patniemeyer/phone-holder/Media/curved2.png

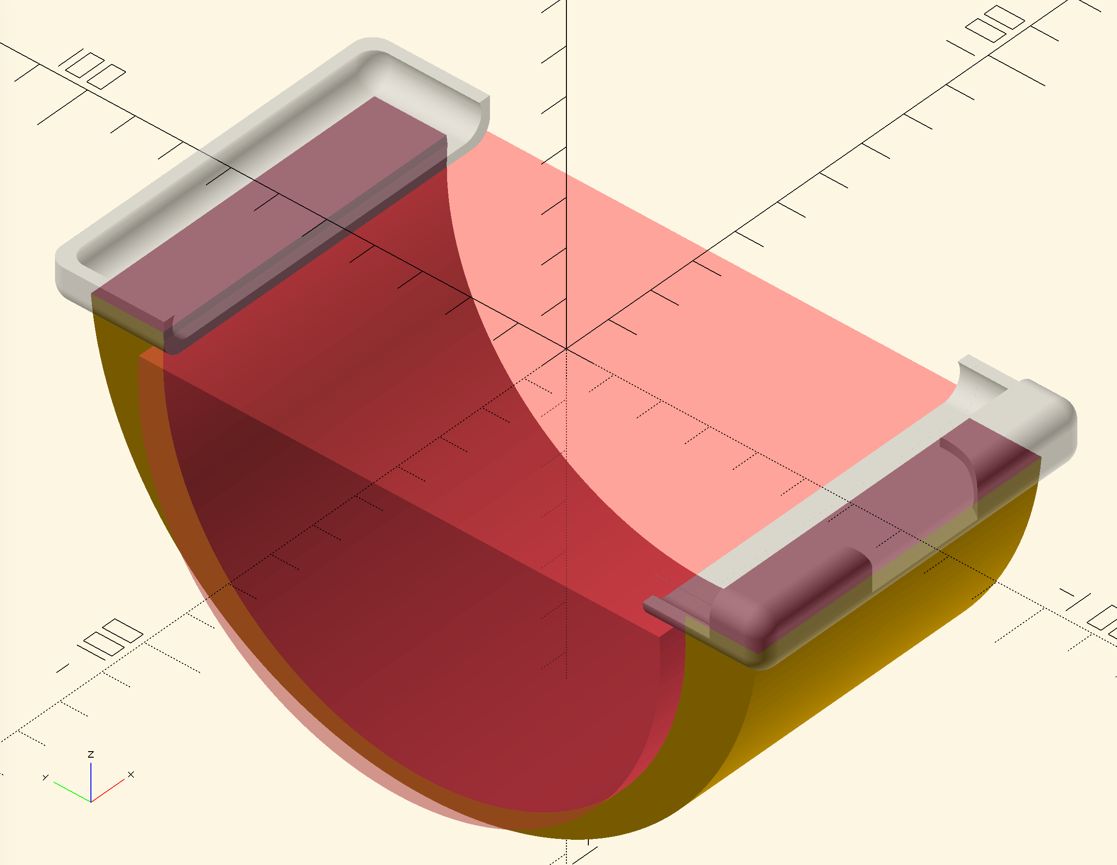
Media/curved2.png
