patniemeyer/phone-holder/Media/IMG_8226.jpg

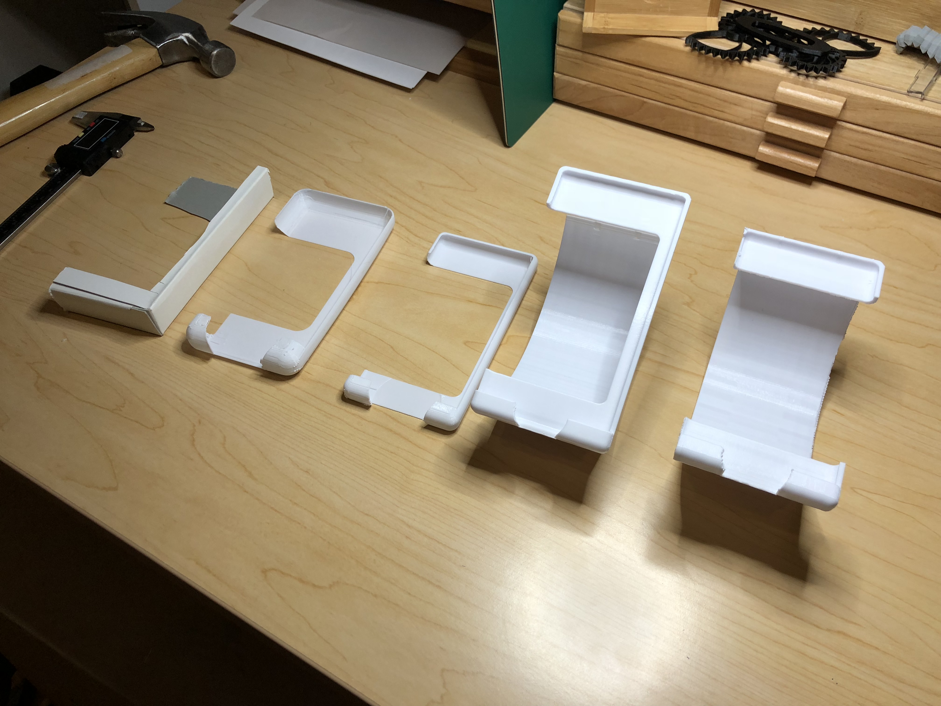
Media/IMG_8226.jpg
