patniemeyer/phone-holder/Media/IMG_9333.jpg

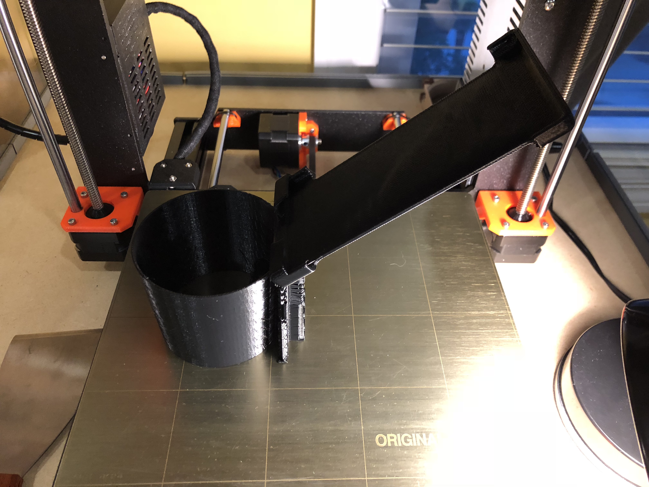
Media/IMG_9333.jpg
