patniemeyer/phone-holder/Media/IMG_9492.jpg

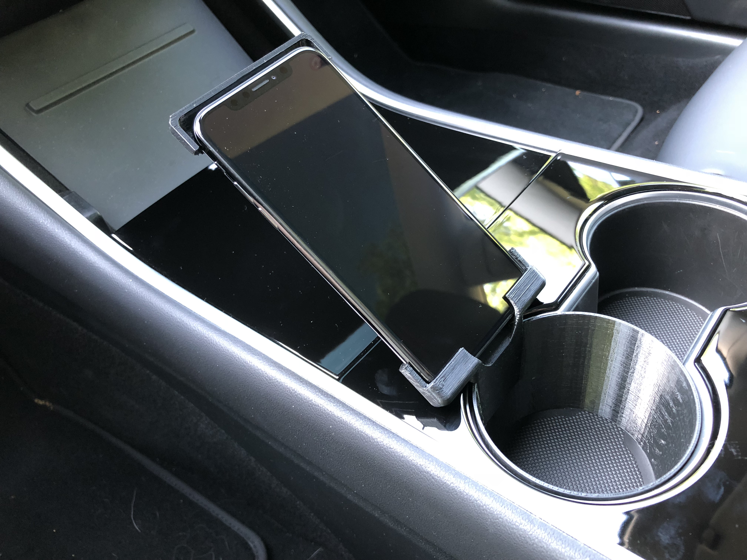
Media/IMG_9492.jpg
