patniemeyer/phone-holder/Media/prototypes2.jpg

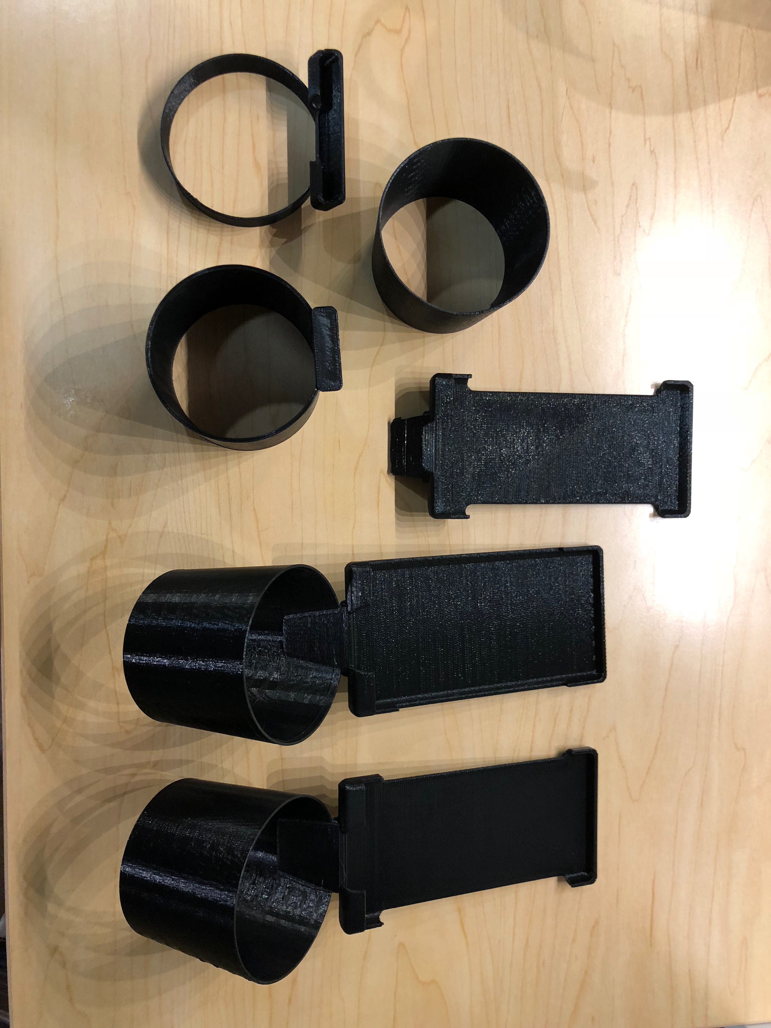
Media/prototypes2.jpg
