patniemeyer/phone-holder/Media/Screen Shot 2018-03-03 at 1.36.28 PM.png

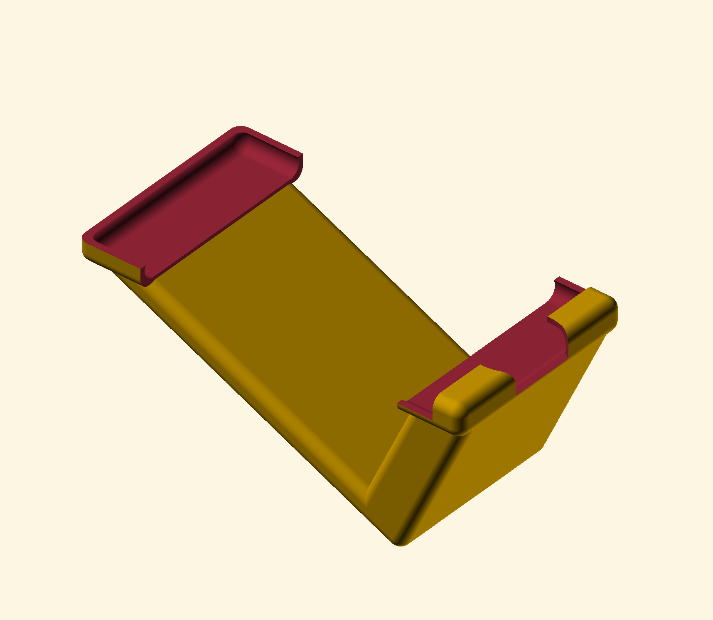
Media/Screen Shot 2018-03-03 at 1.36.28 PM.png
