patniemeyer/phone-holder/Media/Screen Shot 2018-05-19 at 3.50.58 PM.png

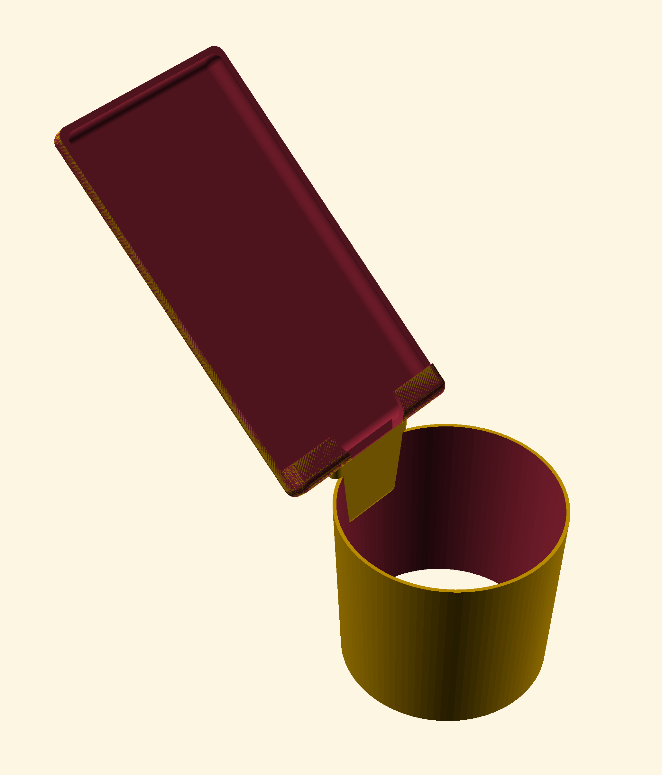
Media/Screen Shot 2018-05-19 at 3.50.58 PM.png
