patniemeyer/phone-holder/Media/wall-holder1.jpg

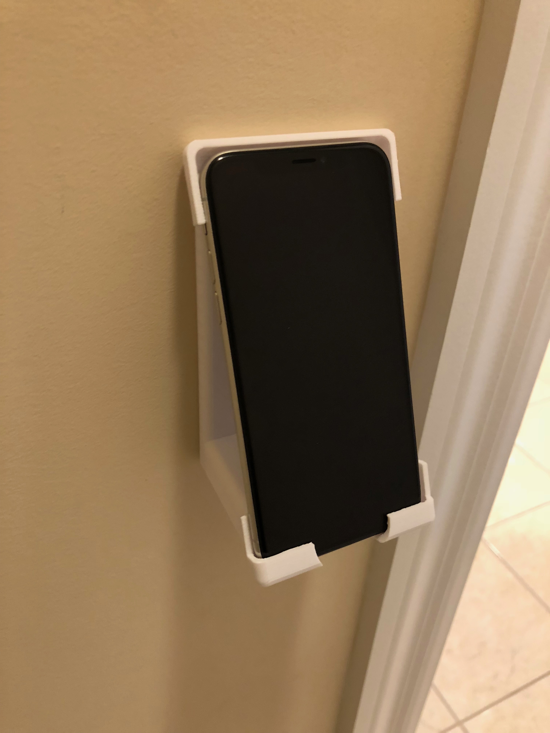
Media/wall-holder1.jpg
