patniemeyer/phone-holder/Media/wall-holder2.jpg

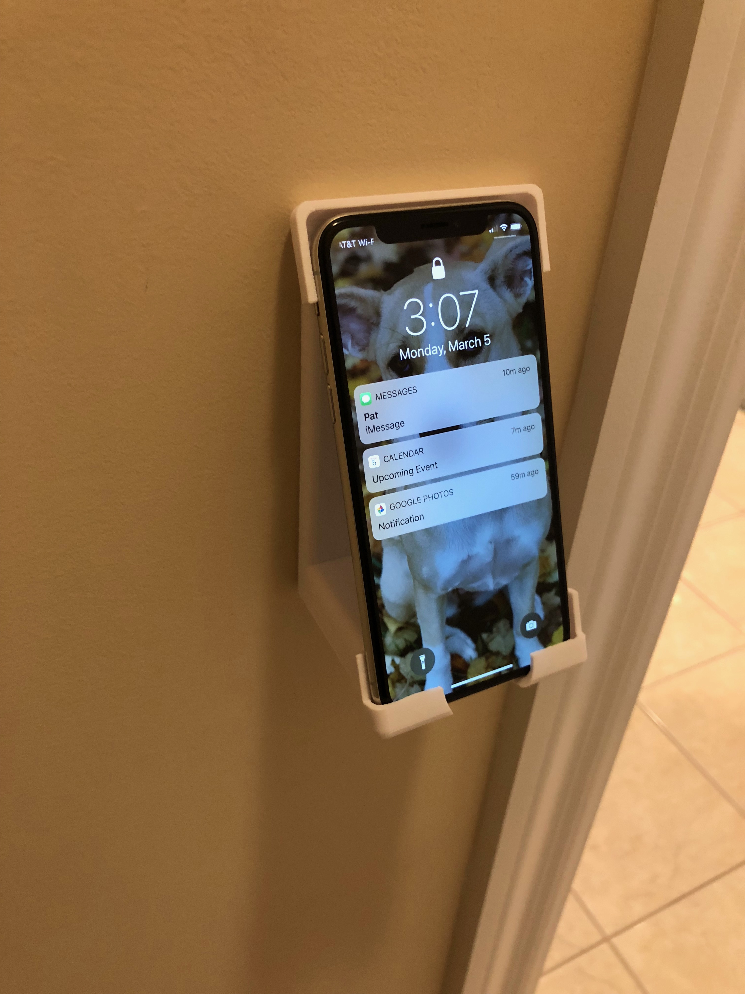
Media/wall-holder2.jpg
