patniemeyer/phone-holder/Media/phone-holder-printed-rough.jpg

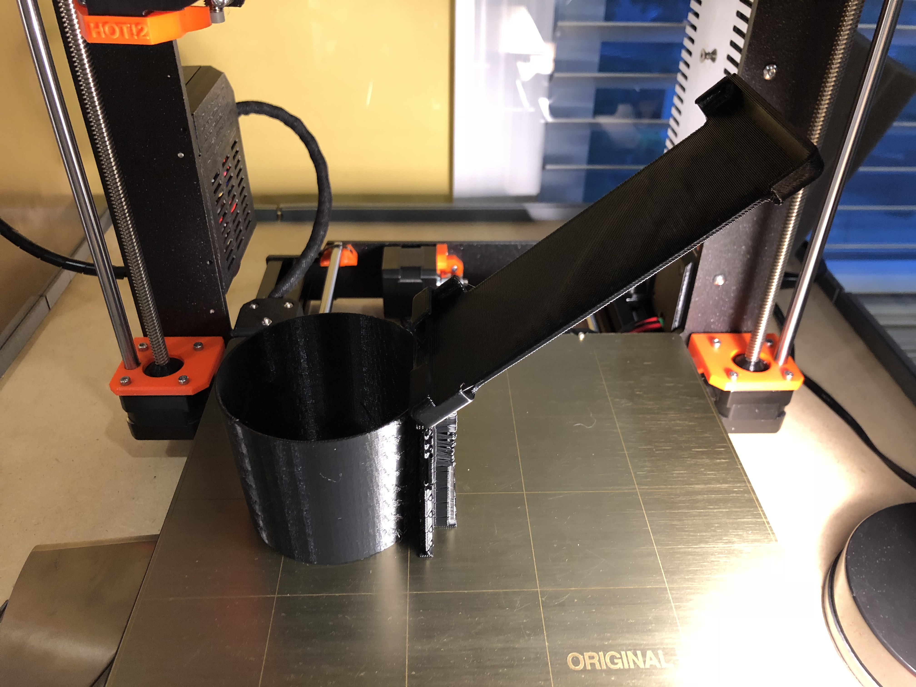
Media/phone-holder-printed-rough.jpg
